rcjcooke/weltec-reactiontester/electronics/schematic.sch

## EAGLE design electronics/schematic.sch (2018-09-19)

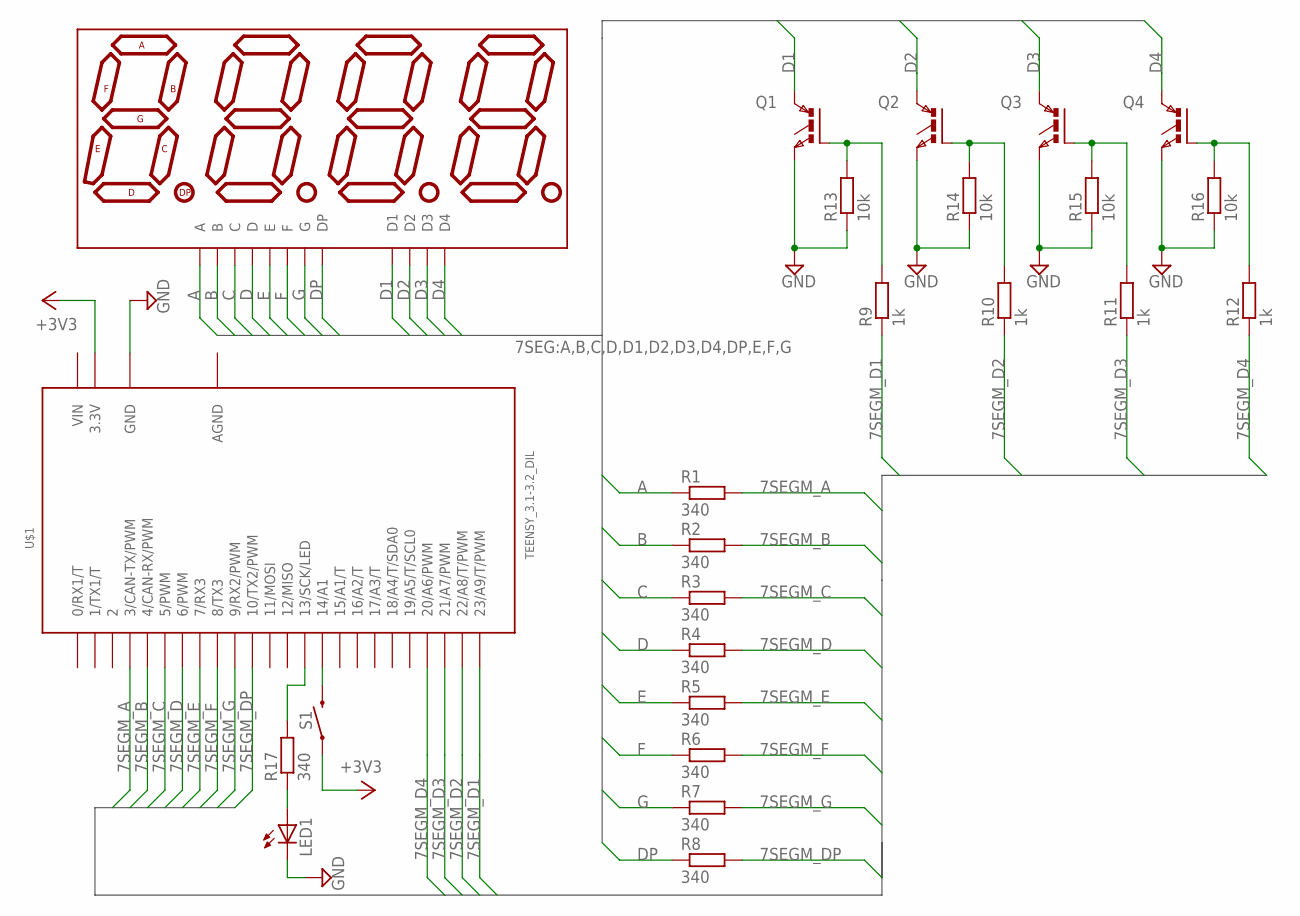
[picture p8: schematic schematic.sch]

Parts:
DISP1: 7-SEGMENT-4DIGIT-COUNTER-HP-BUBBLE; DIL12
LED1: LED_ELD260; LED_LD260
Q1, Q2, Q3, Q4: IGBTTO251AA; TO251AA
R1, R2, R3, R4, R5, R6, R7, R8, R17: 340; 0204/5
R9, R10, R11, R12: 1k; 0204/5
R13, R14, R15, R16: 10k; 0204/5
S1: MOMENTARY-SWITCH-SPST-PTH-6.0MM; TACTILE_SWITCH_PTH_6.0MM
U$1: TEENSY_3.1-3.2_DIL; TEENSY_3.0-3.2&LC_DIL

Connections:
7SEGM_A: R1.2, U$1.3 (3/CAN-TX/PWM)
7SEGM_B: R2.2, U$1.4 (4/CAN-RX/PWM)
7SEGM_C: R3.2, U$1.5 (5/PWM)
7SEGM_D: R4.2, U$1.6 (6/PWM)
7SEGM_D1: R9.1, U$1.23/A9 (23/A9/T/PWM)
7SEGM_D2: R10.1, U$1.22/A8 (22/A8/T/PWM)
7SEGM_D3: R11.1, U$1.21/A7 (21/A7/PWM)
7SEGM_D4: R12.1, U$1.20/A6 (20/A6/PWM)
7SEGM_DP: R8.2, U$1.10 (10/TX2/PWM)
7SEGM_E: R5.2, U$1.7 (7/RX3)
7SEGM_F: R6.2, U$1.8 (8/TX3)
7SEGM_G: R7.2, U$1.9 (9/RX2/PWM)
+3V3: S1.1, U$1.3.3V
A: DISP1.12 (A), R1.1
B: DISP1.11 (B), R2.1
C: DISP1.3 (C), R3.1
D: DISP1.8 (D), R4.1
D1: DISP1.1 (D1), Q1.2 (C)
D2: DISP1.10 (D2), Q2.2 (C)
D3: DISP1.4 (D3), Q3.2 (C)
D4: DISP1.6 (D4), Q4.2 (C)
DP: DISP1.5 (DP), R8.1
E: DISP1.2 (E), R5.1
F: DISP1.9 (F), R6.1
G: DISP1.7 (G), R7.1
GND: LED1.K (C), Q1.3 (E), Q2.3 (E), Q3.3 (E), Q4.3 (E), R13.1, R14.1, R15.1, R16.1, U$1.GND
unnamed: Q1.1 (G), R9.2, R13.2
unnamed: S1.3 (2), U$1.14/A0 (14/A1)
unnamed: R17.2, U$1.13 (13/SCK/LED)
unnamed: Q2.1 (G), R10.2, R14.2
unnamed: LED1.A, R17.1
unnamed: Q3.1 (G), R11.2, R15.2
unnamed: Q4.1 (G), R12.2, R16.2
